vi-robotics/phonebot_board/design/figs/PhoneBotFront.png

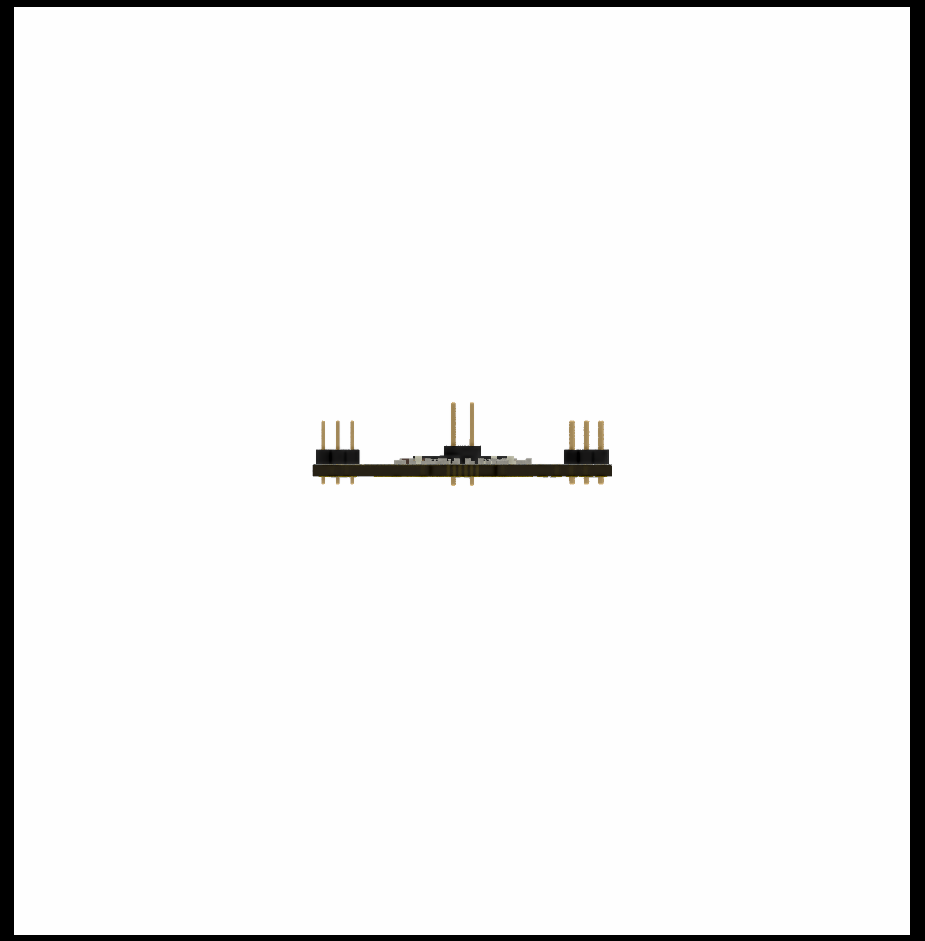
design/figs/PhoneBotFront.png
